norahueppi/Marvin/5_Semester/documentation/Earphone_Plug.png

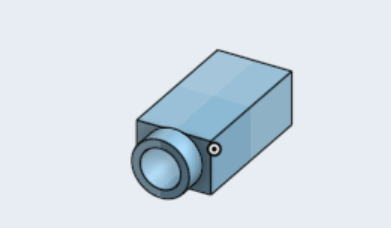
5_Semester/documentation/Earphone_Plug.png
