norahueppi/Marvin/5_Semester/documentation/Vero_Board.png

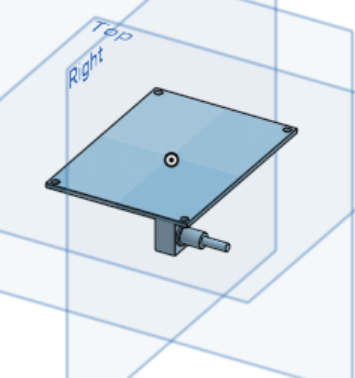
5_Semester/documentation/Vero_Board.png
